tebl/RC-ONE/software/examples/FBK-Movit/movit.pdf

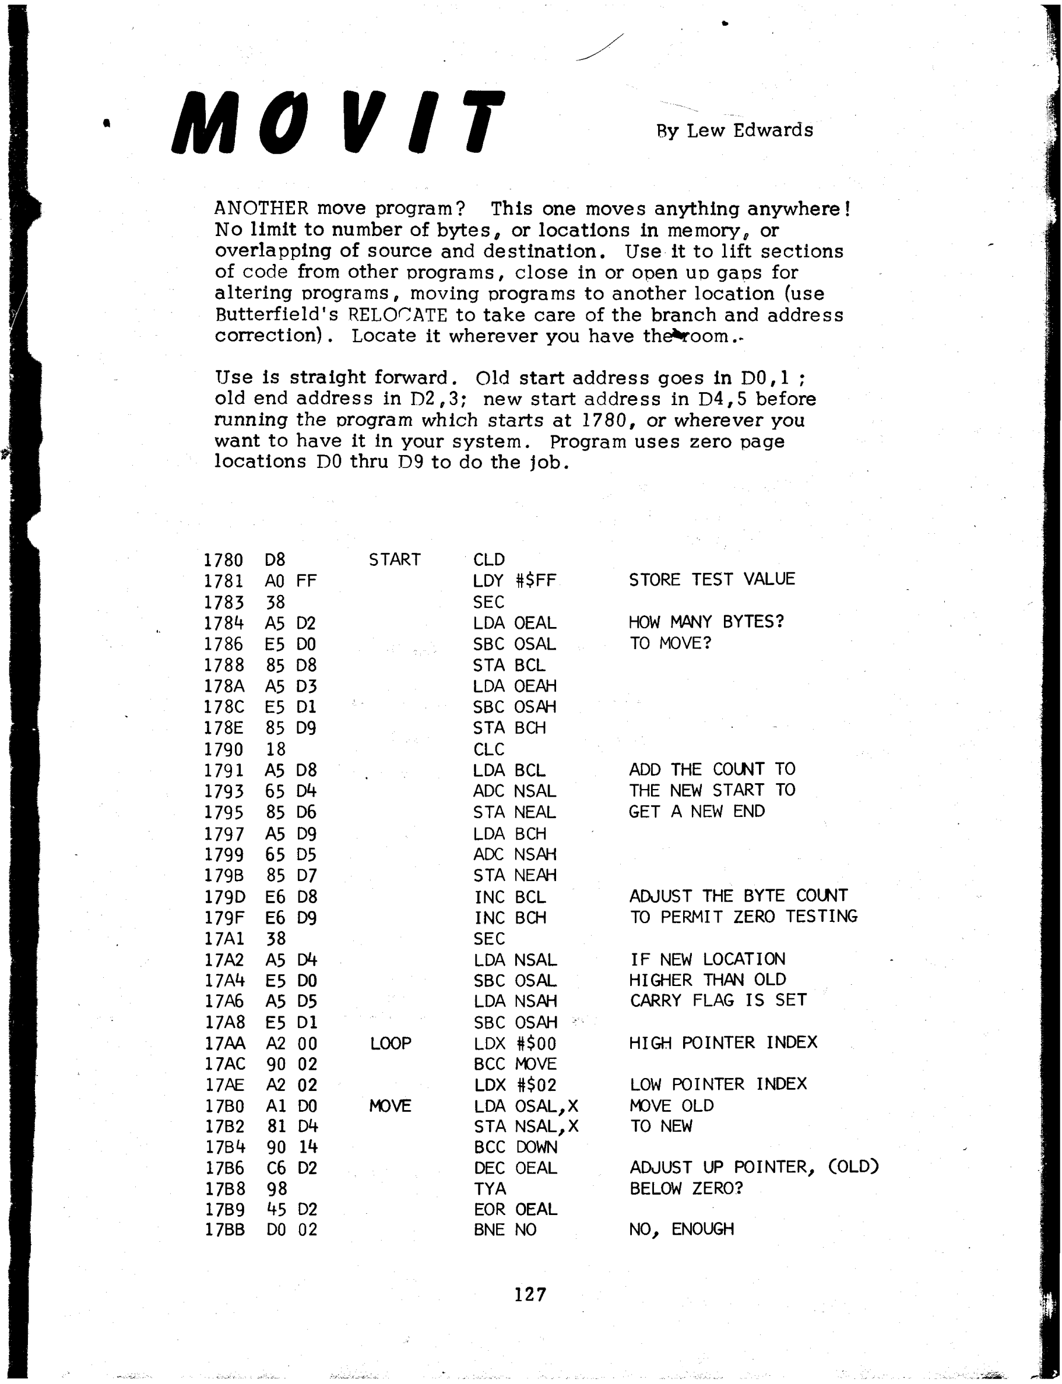
[picture p11: page 1]
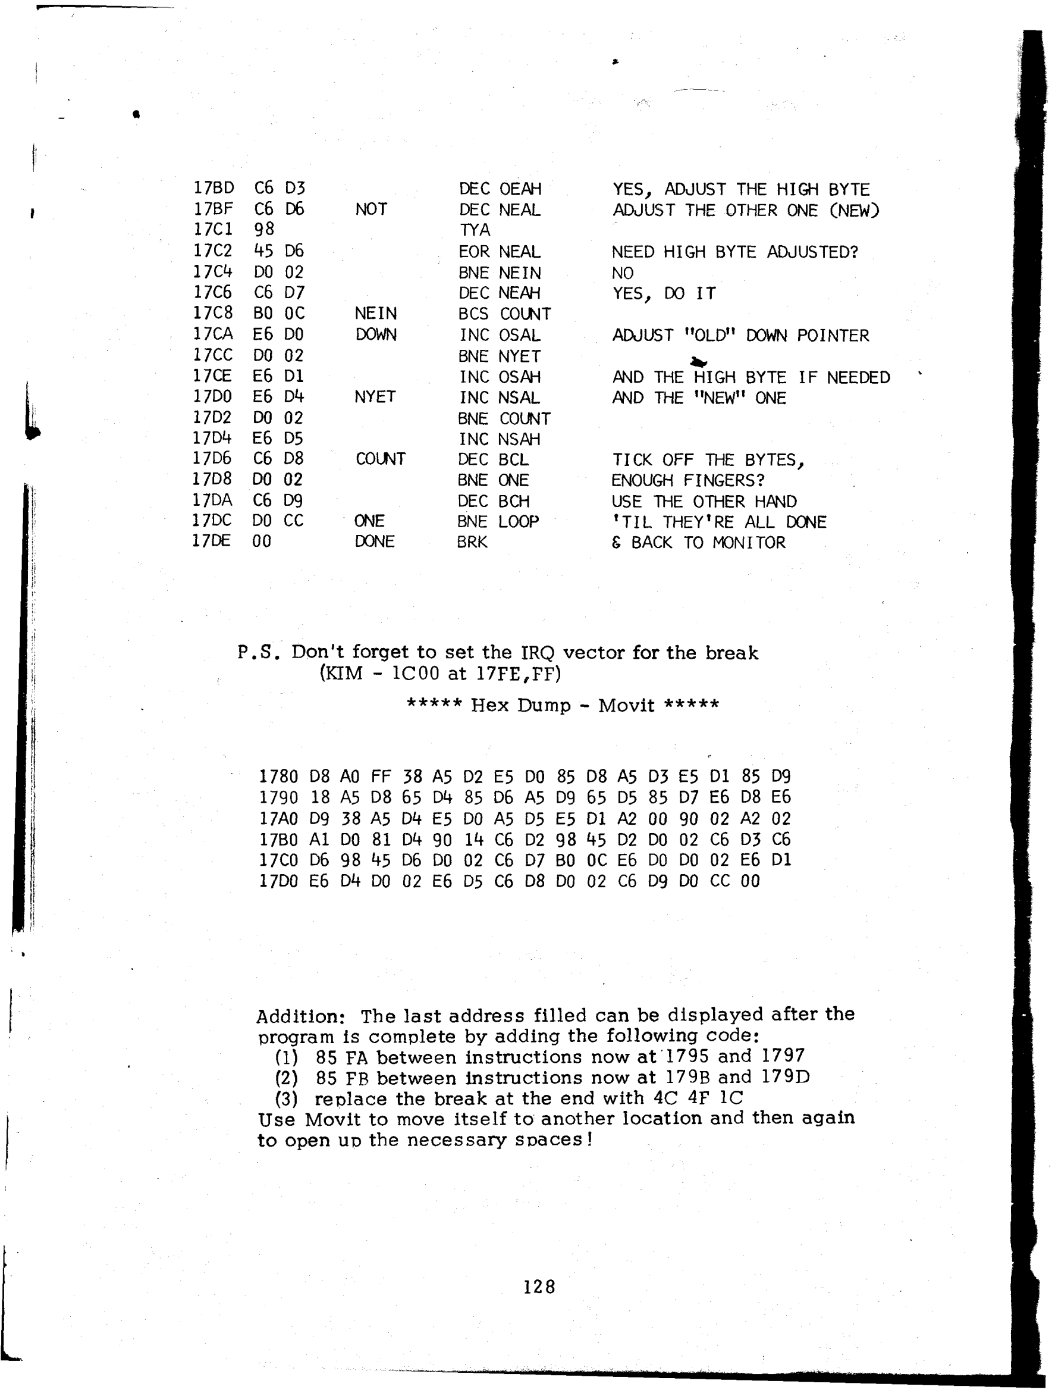
[picture p12: page 2]
