tebl/RC-ONE/gallery/2019-10-24 20.48.41.jpg

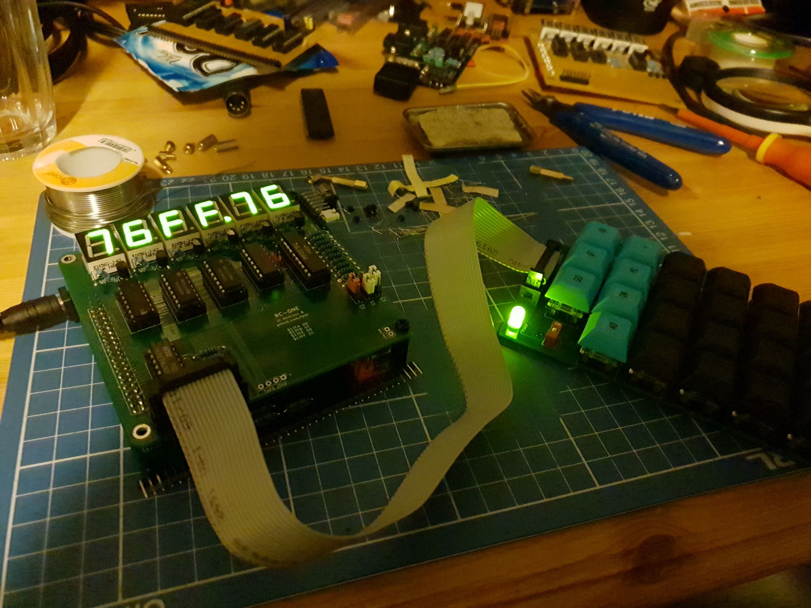
gallery/2019-10-24 20.48.41.jpg
