tebl/RC-ONE/gallery/2019-11-24 02.01.32.jpg

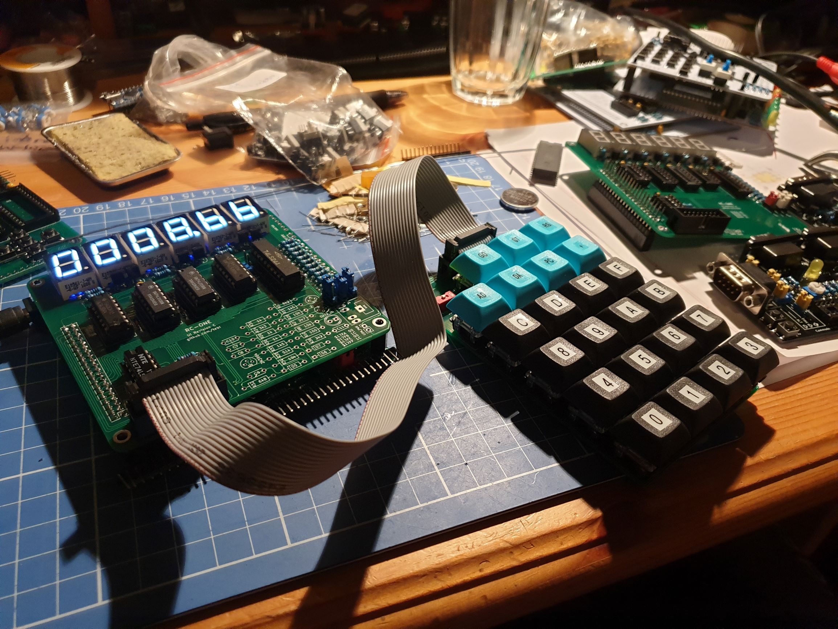
gallery/2019-11-24 02.01.32.jpg
