tebl/RC-ONE/RC1 8K ExRAM/gallery/Annotation 2020-01-12 215217.png

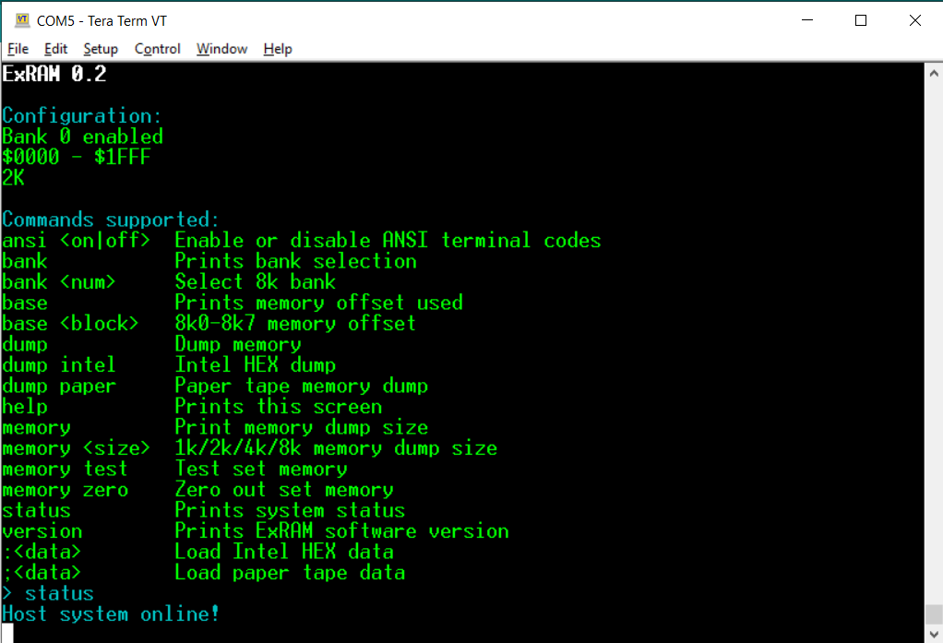
RC1 8K ExRAM/gallery/Annotation 2020-01-12 215217.png
