tebl/RC-ONE/RC1 8K ExRAM/gallery/Annotation 2020-01-12 215605.png

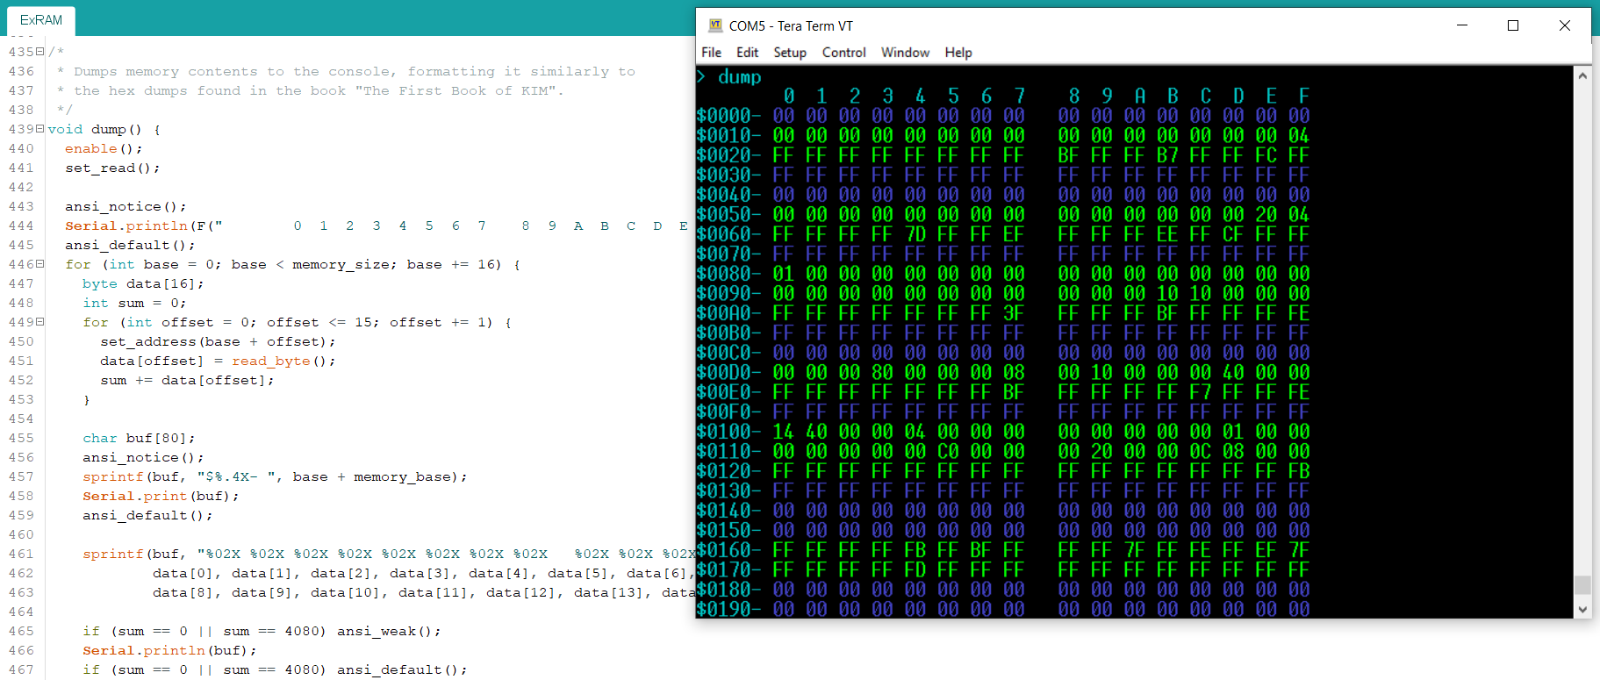
RC1 8K ExRAM/gallery/Annotation 2020-01-12 215605.png
