tebl/RC-ONE/RC1 8K ExRAM/gallery/Annotation 2020-01-13 213625.png

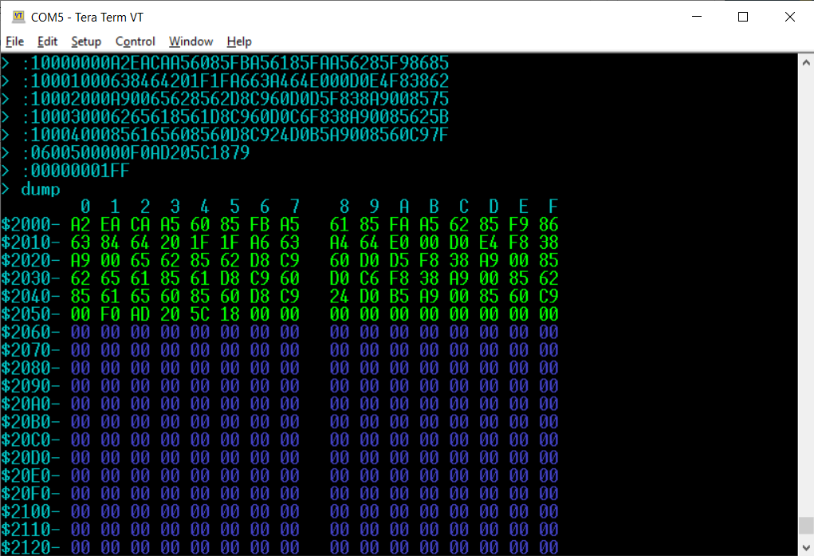
RC1 8K ExRAM/gallery/Annotation 2020-01-13 213625.png
