tebl/RC-ONE/RC1 8K ExRAM/gallery/RC1 8K ExRAM.png

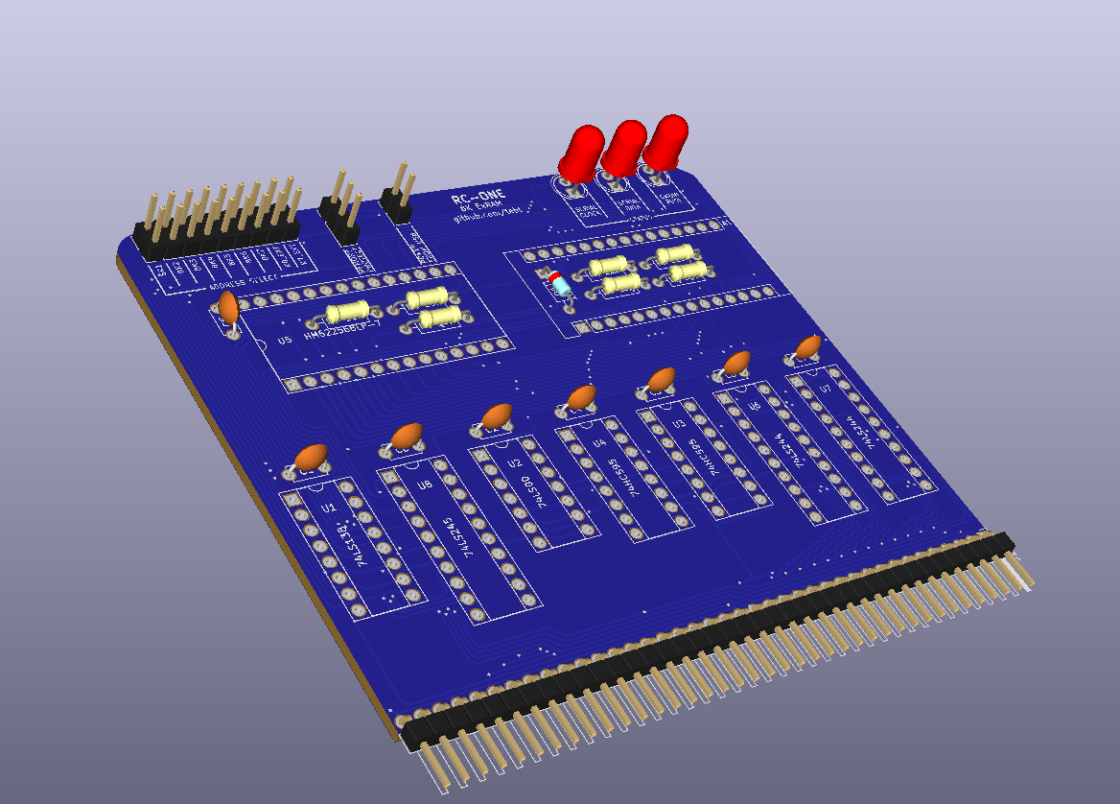
RC1 8K ExRAM/gallery/RC1 8K ExRAM.png
