tebl/RC-ONE/RC1 65K Expansion/gallery/application_io.png

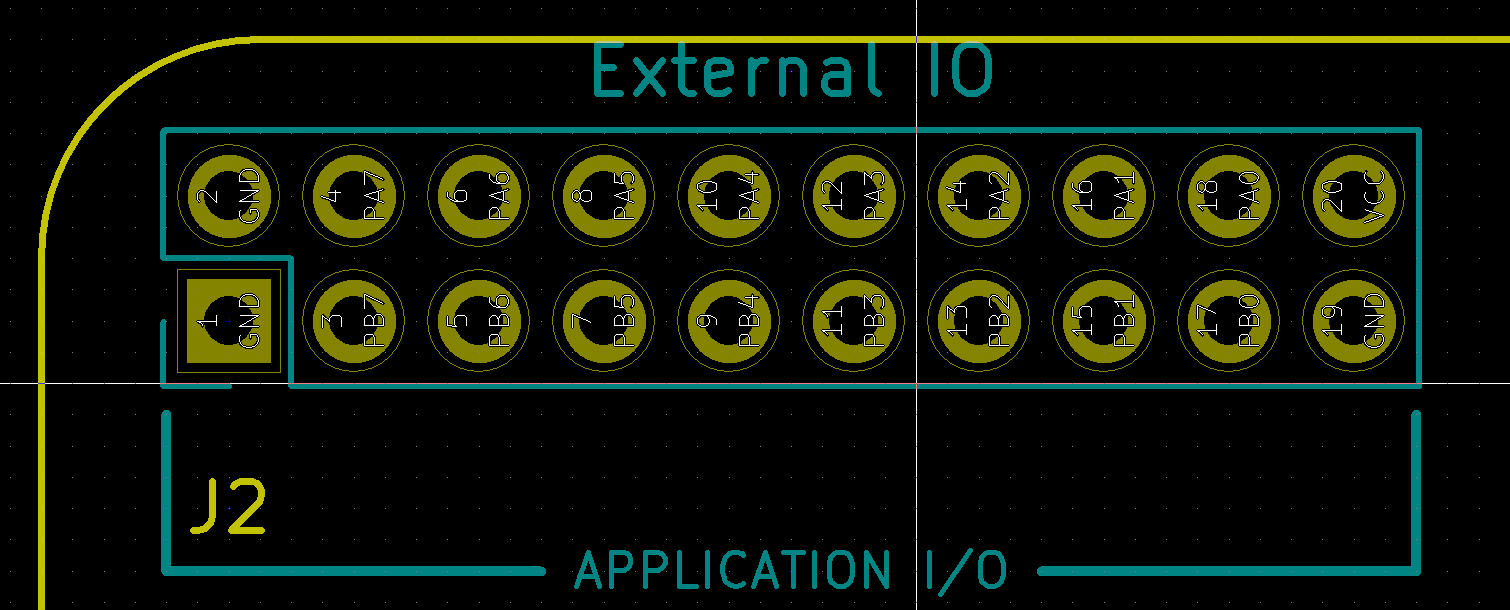
RC1 65K Expansion/gallery/application_io.png
