tebl/RC-ONE/RC1 65K Expansion/gallery/RC1 65K Expansion.png

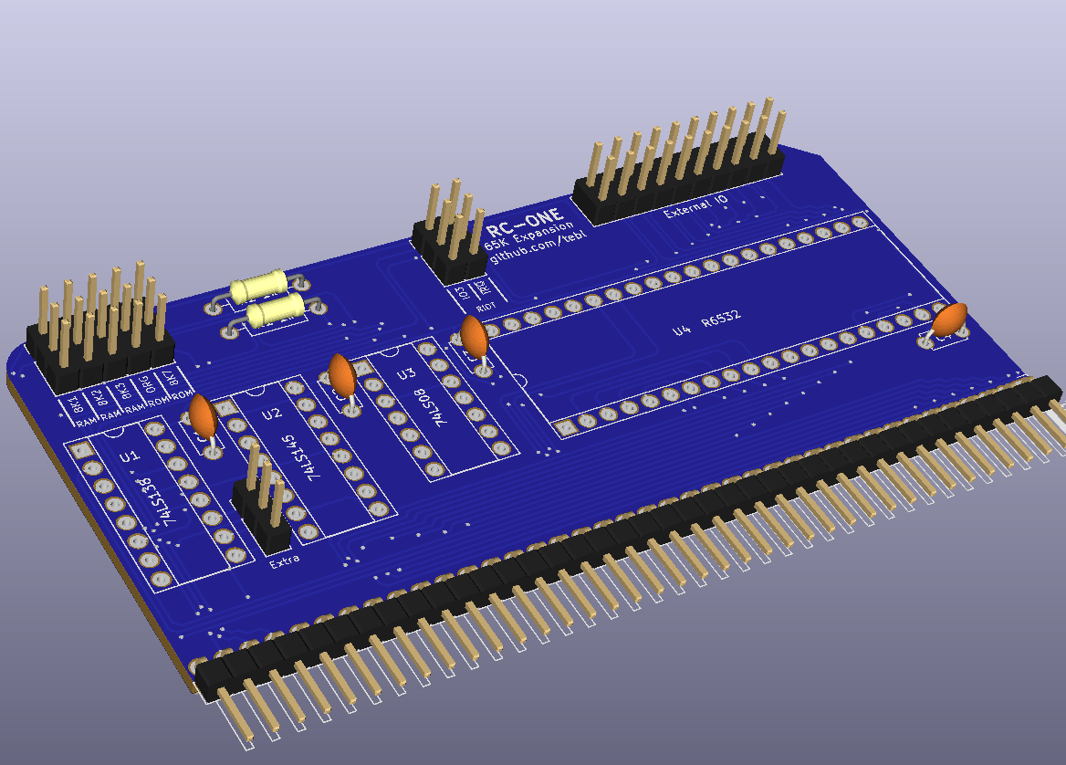
RC1 65K Expansion/gallery/RC1 65K Expansion.png
