tebl/RC-ONE/RC1 ACIA/gallery/2020-10-18 02.24.50.jpg

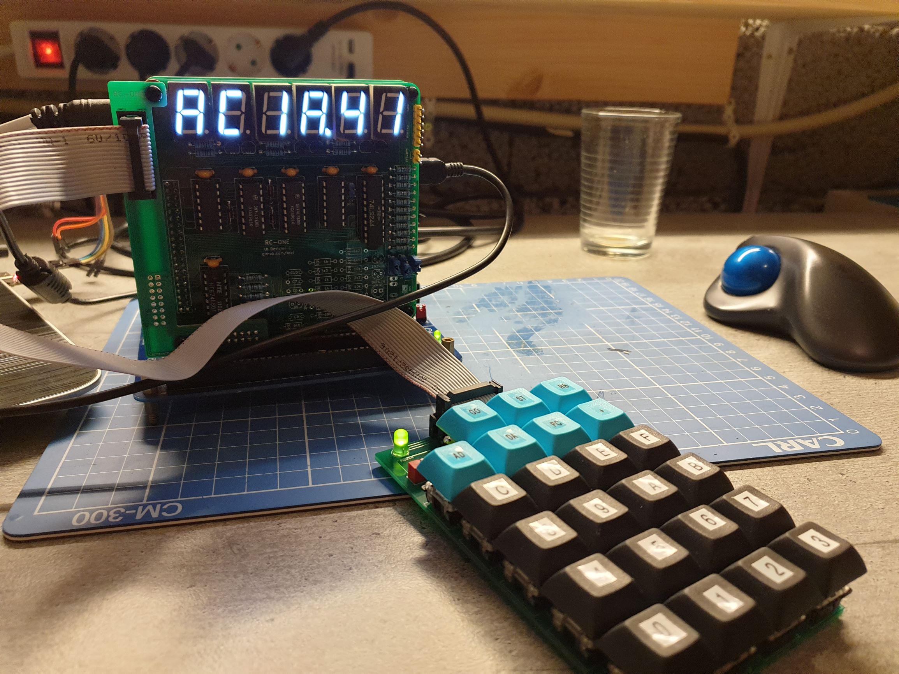
RC1 ACIA/gallery/2020-10-18 02.24.50.jpg
