tebl/RC-ONE/RC1 ACIA/gallery/tera_term_001.png

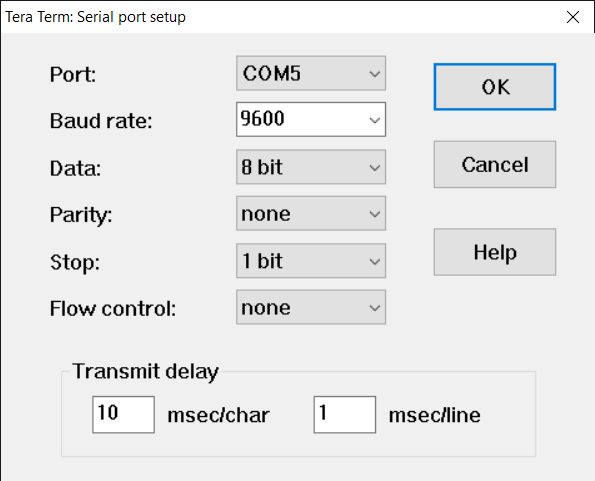
RC1 ACIA/gallery/tera_term_001.png
