tebl/RC-ONE/RC1 ACIA/gallery/tera_term_002.png

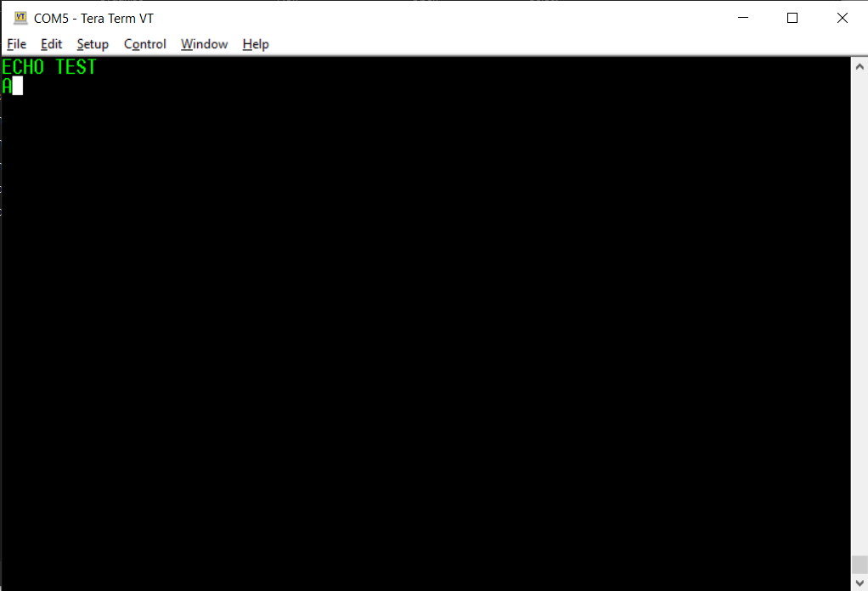
RC1 ACIA/gallery/tera_term_002.png
