tebl/RC-ONE/RC1 CPU/gallery/2019-10-21 21.03.31.jpg

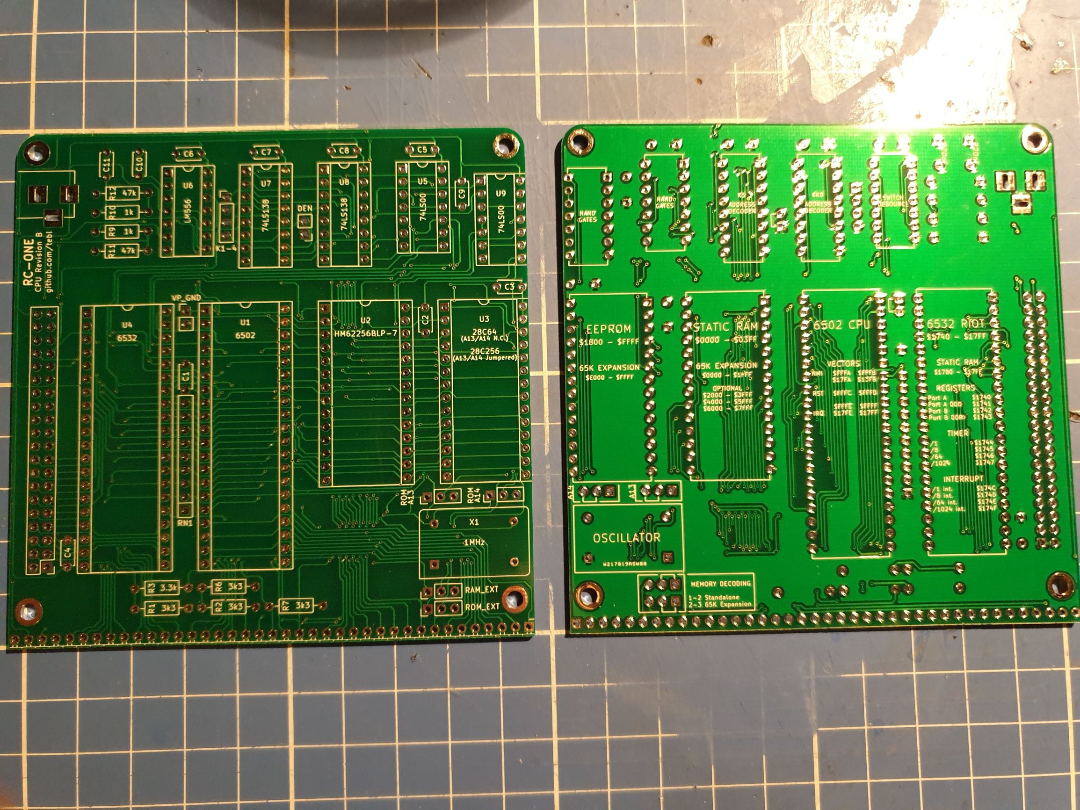
RC1 CPU/gallery/2019-10-21 21.03.31.jpg
