tebl/RC-ONE/RC1 Keypad MX/gallery/2019-10-21 21.00.52.jpg

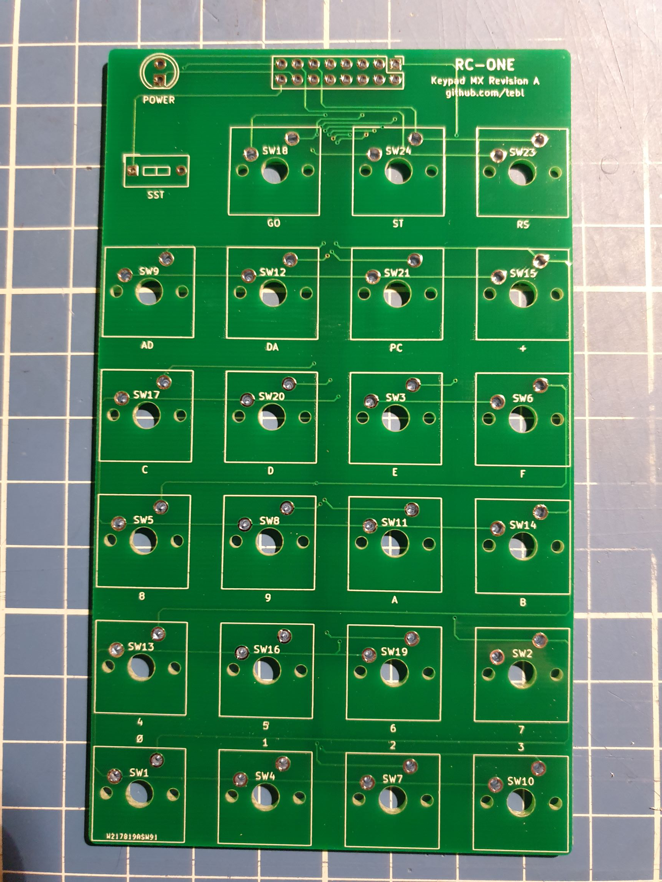
RC1 Keypad MX/gallery/2019-10-21 21.00.52.jpg
