tebl/RC-ONE/RC1 Sound Interface/gallery/RC1 Sound Interface #2.png

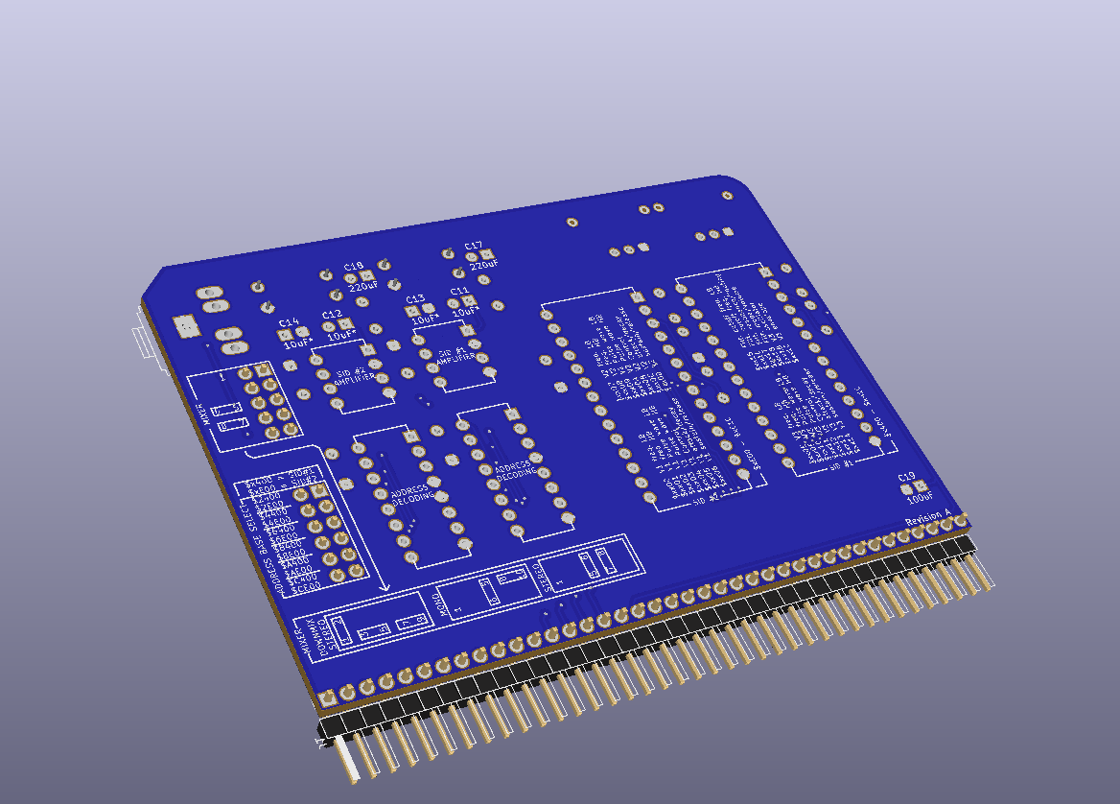
RC1 Sound Interface/gallery/RC1 Sound Interface #2.png
