tebl/RC-ONE/RC1 UI/gallery/2019-10-21 21.02.37.jpg

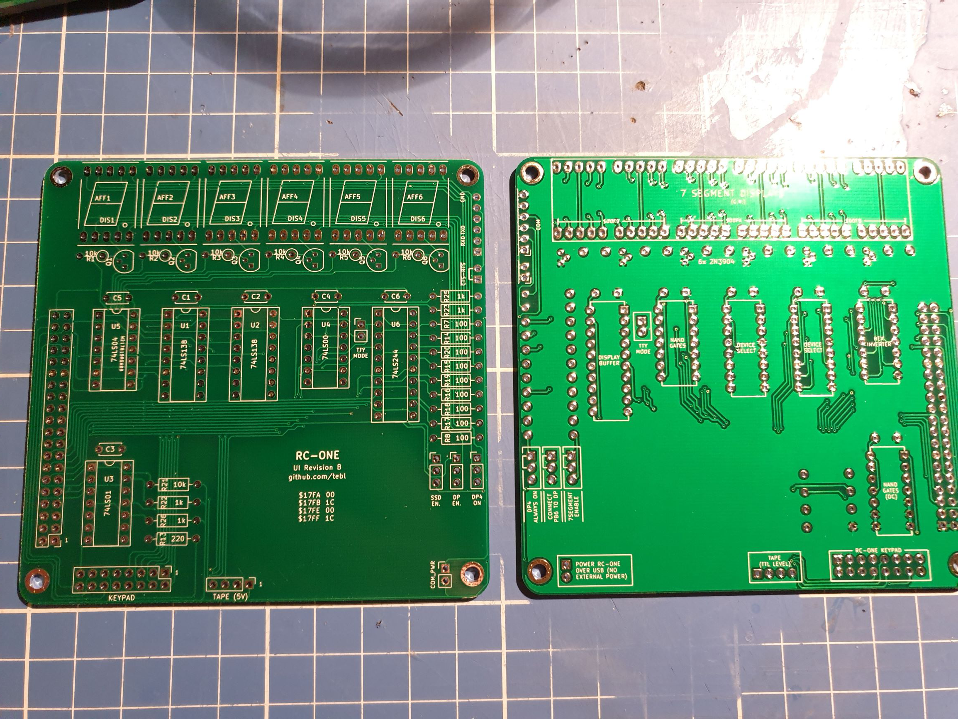
RC1 UI/gallery/2019-10-21 21.02.37.jpg
