tebl/RC-ONE/RC1 Keypad/export/RC1 Keypad.pdf

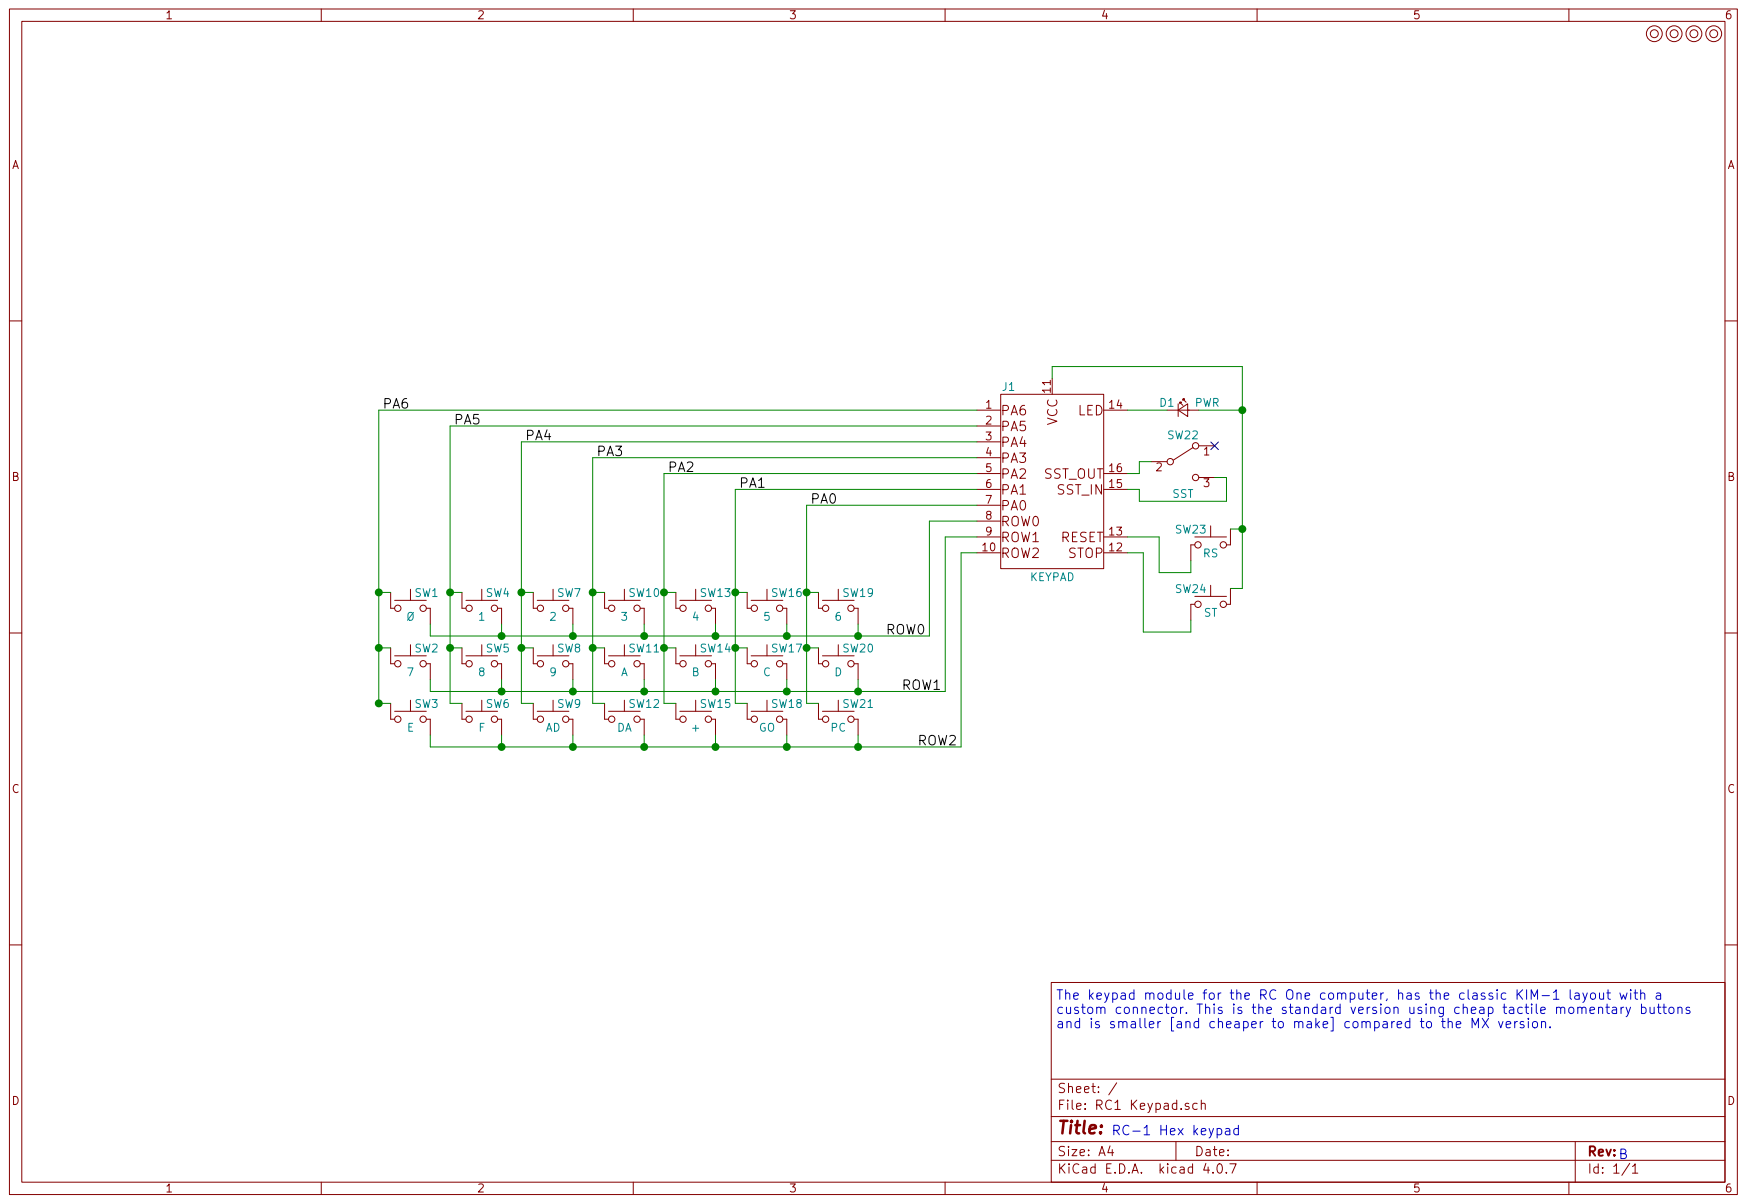
[picture p54: page 1]
