tebl/RC-ONE/RC1 CPU/export/RC1 CPU.pdf

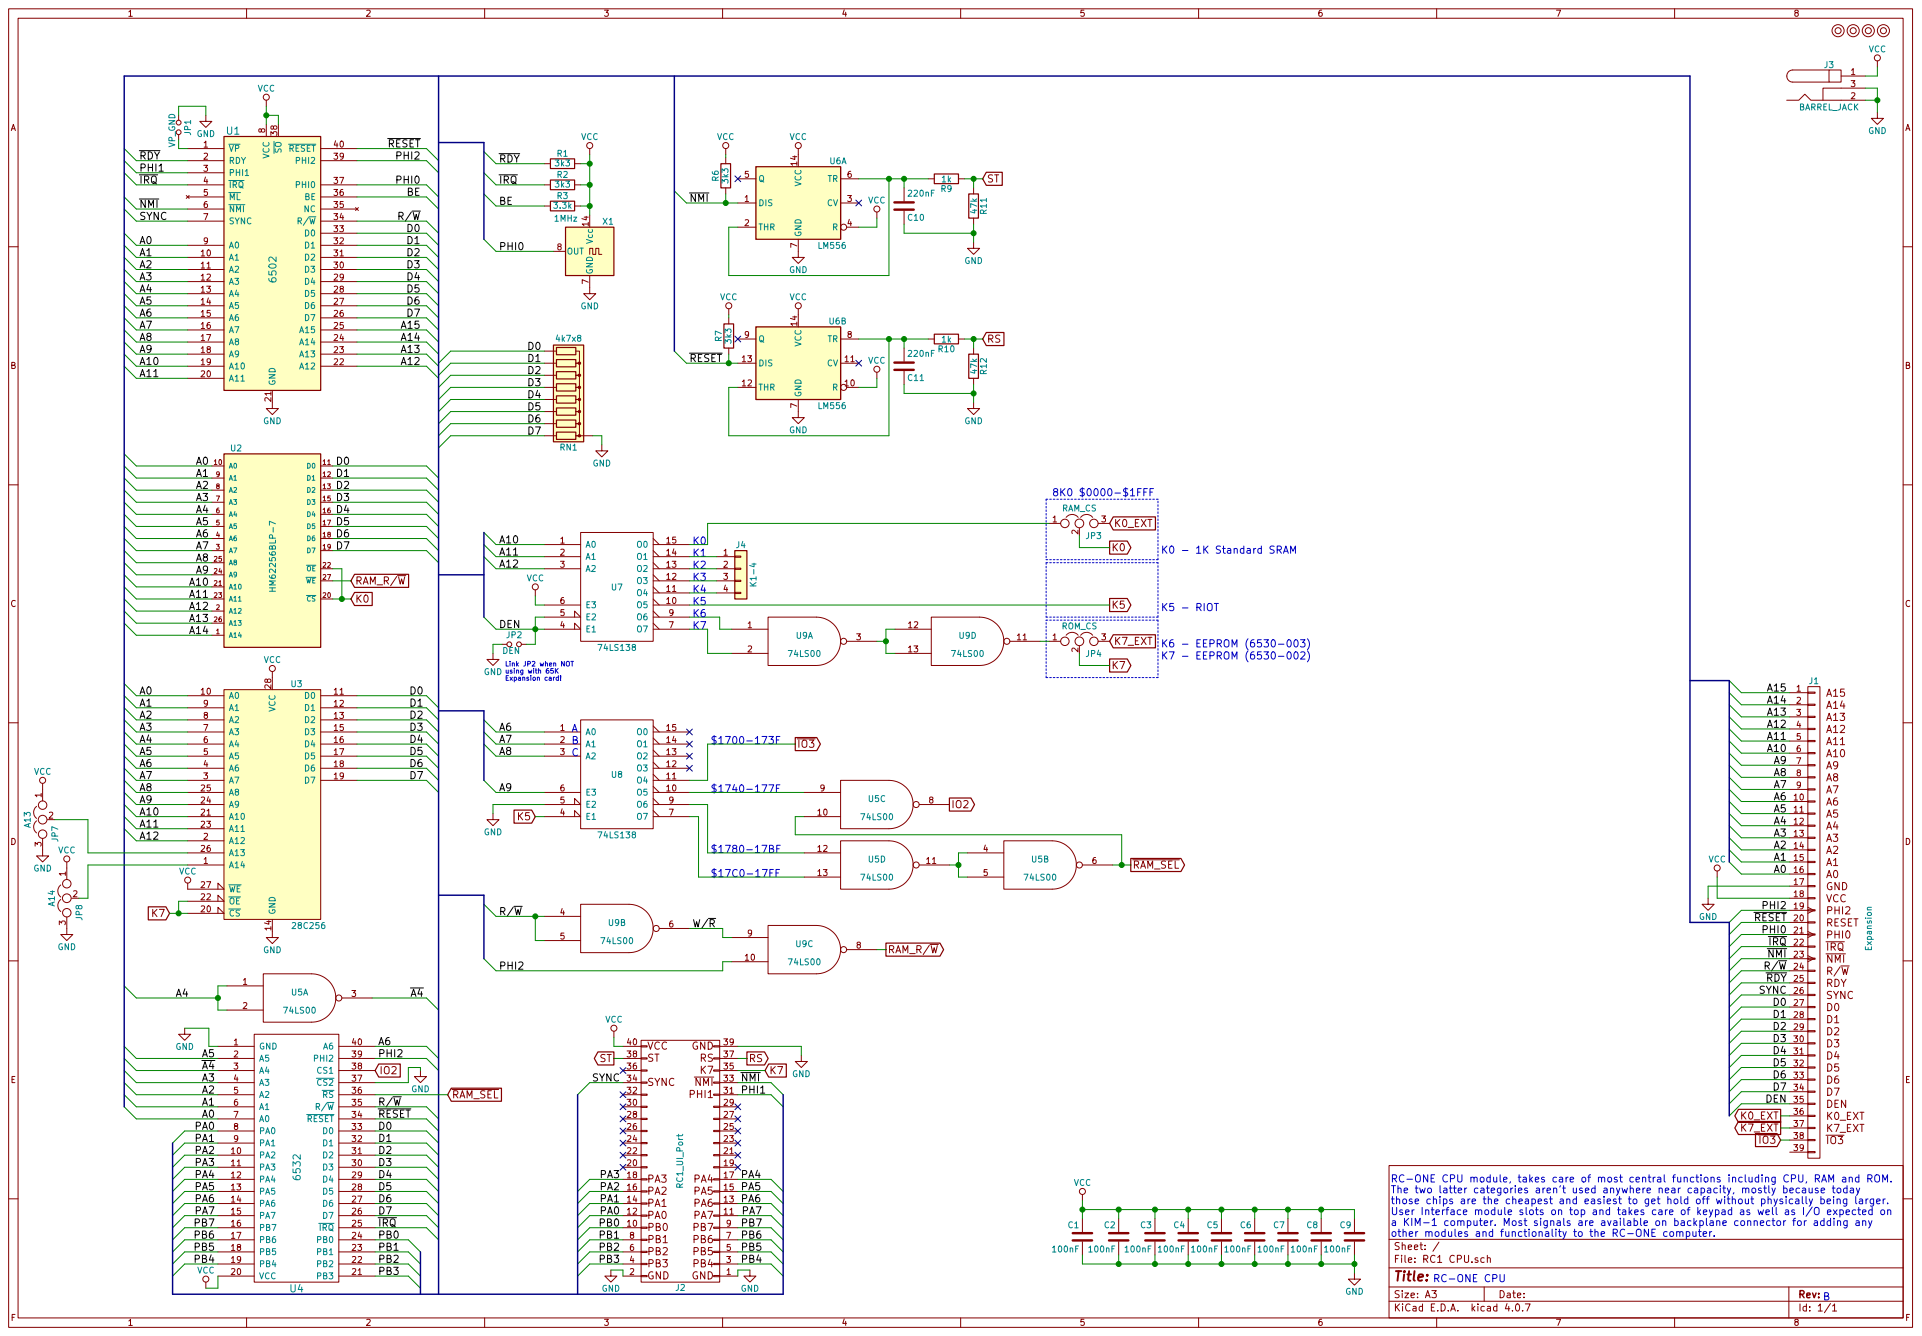
[picture p55: page 1]
