tebl/RC-ONE/RC1 UI/RC1 UI.kicad_pcb

## KiCad design RC1 UI/RC1 UI.kicad_pcb (2019-11-08)

Schematic: RC1 UI-2020-03-10-23-34-16.sch

Parts:
AFF1: DIS1; 7SegmentLED_LTS6760_LTS6780
AFF2: DIS2; 7SegmentLED_LTS6760_LTS6780
AFF3: DIS3; 7SegmentLED_LTS6760_LTS6780
AFF4: DIS4; 7SegmentLED_LTS6760_LTS6780
AFF5: DIS5; 7SegmentLED_LTS6760_LTS6780
AFF6: DIS6; 7SegmentLED_LTS6760_LTS6780
C1, C2, C3, C4, C5, C6, C11: 100nF; C_Disc_D4.7mm_W2.5mm_P5.00mm
C7, C9: 50nF; C_Disc_D4.7mm_W2.5mm_P5.00mm
C8: 68nF; C_Disc_D4.7mm_W2.5mm_P5.00mm
C10: 500nF; C_Disc_D4.7mm_W2.5mm_P5.00mm
D1, D2, D3: 1n4148; D_DO-35_SOD27_P7.62mm_Horizontal
D4: DATA_IN; LED_D5.0mm
D5, D6, D7: 1n914; D_DO-35_SOD27_P7.62mm_Horizontal
J1: KEYPAD; Pin_Header_Straight_2x08_Pitch2.54mm
J2: RC1_UI_Port; Pin_Header_Straight_2x20_Pitch2.54mm
J3: COM; Pin_Header_Angled_1x06_Pitch2.54mm
J4: TAPE; Tayda_3.5mm_stereo_TRS_jack_A-853
JP1: COM_PWR; Pin_Header_Straight_1x02_Pitch2.54mm
JP2: FlowControl; Pin_Header_Angled_1x02_Pitch2.54mm
JP3: USE_COM; Pin_Header_Straight_1x02_Pitch2.54mm
JP4: DP_EN; Pin_Header_Straight_1x03_Pitch2.54mm
JP5: SSD_EN; Pin_Header_Straight_1x03_Pitch2.54mm
JP6: DP4_EN; Pin_Header_Straight_1x03_Pitch2.54mm
M1, M2, M3, M4: Mounting; 1pin
Q1, Q2, Q3, Q4, Q5, Q6, Q7, Q8, Q9: 2N3904; TO-92_Molded_Narrow
R1, R2, R3, R4, R5, R6, R9, R21, R28, R34: 10k; R_Axial_DIN0207_L6.3mm_D2.5mm_P10.16mm_Horizontal
R7, R8, R10, R14, R15, R16, R17, R18, R19, R20: 100; R_Axial_DIN0207_L6.3mm_D2.5mm_P10.16mm_Horizontal
R11, R33: 1k5; R_Axial_DIN0207_L6.3mm_D2.5mm_P10.16mm_Horizontal
R12: 6k2; R_Axial_DIN0207_L6.3mm_D2.5mm_P10.16mm_Horizontal
R13: 220; R_Axial_DIN0207_L6.3mm_D2.5mm_P10.16mm_Horizontal
R22, R23, R25, R26, R29, R30, R31: 1k; R_Axial_DIN0207_L6.3mm_D2.5mm_P10.16mm_Horizontal
R24: 3k3; R_Axial_DIN0207_L6.3mm_D2.5mm_P10.16mm_Horizontal
R27: 2k7; R_Axial_DIN0207_L6.3mm_D2.5mm_P10.16mm_Horizontal
R32: 6k8; R_Axial_DIN0207_L6.3mm_D2.5mm_P10.16mm_Horizontal
R35: 51k; R_Axial_DIN0207_L6.3mm_D2.5mm_P10.16mm_Horizontal
R36: 2k2; R_Axial_DIN0207_L6.3mm_D2.5mm_P10.16mm_Horizontal
U1, U2: 74LS138; DIP-16_W7.62mm_Socket
U3: 74LS01; DIP-14_W7.62mm_Socket
U4: 74LS00; DIP-14_W7.62mm_Socket
U5: 74LS04; DIP-14_W7.62mm_Socket
U6: 74LS244; DIP-20_W7.62mm_Socket

Connections:
/A: AFF1.7, AFF2.7, AFF3.7, AFF4.7, AFF5.7, AFF6.7, R14.2
/B: AFF1.6, AFF2.6, AFF3.6, AFF4.6, AFF5.6, AFF6.6, R15.2
/C: AFF1.4, AFF2.4, AFF3.4, AFF4.4, AFF5.4, AFF6.4, R16.2
/D: AFF1.2, AFF2.2, AFF3.2, AFF4.2, AFF5.2, AFF6.2, R17.2
/DIS1: R1.2, U5.2
/DIS2: R2.2, U5.4
/DIS3: R3.2, U5.6
/DIS4: R4.2, U5.8
/DIS5: R5.2, U5.10
/DIS6: R6.2, U5.12
/DP: AFF1.5, AFF2.5, AFF3.5, AFF5.5, AFF6.5, JP6.3, R7.2
/DP4: AFF4.5, JP6.2
/E: AFF1.1, AFF2.1, AFF3.1, AFF4.1, AFF5.1, AFF6.1, R18.2
/F: AFF1.9, AFF2.9, AFF3.9, AFF4.9, AFF5.9, AFF6.9, R19.2
/G: AFF1.10, AFF2.10, AFF3.10, AFF4.10, AFF5.10, AFF6.10, R20.2
/KP_RS: J1.13, J2.37
/KP_ST: J1.12, J2.38
/MODE: JP3.2, U1.12 (O3)
/PA0: J1.7, J2.12, JP3.1, U6.2 (I0a)
/PA1: J1.6, J2.14, U6.4 (I1a)
/PA2: J1.5, J2.16, U6.6 (I2a)
/PA3: J1.4, J2.18, U6.8 (I3a)
/PA4: J1.3, J2.17, U6.11 (I0b)
/PA5: J1.2, J2.15, U6.13 (I1b)
/PA6: J1.1, J2.13, U6.15 (I2b)
/PA7: J2.11, U4.6, U4.9
/PB0: J2.10, U4.10
/PB1: J2.8, U1.1 (A0), U2.1 (A0)
/PB2: J2.6, U1.2 (A1), U2.2 (A1)
/PB3: J2.4, U1.3 (A2), U2.3 (A2)
/PB4: J2.3, U1.5 (E2), U2.6 (E3)
/PB5: J2.5, U4.1, U4.2
/PB6: J2.7, JP4.1
/PB7: J2.9, U3.12, U4.11
/ROW0: D3.2, J1.8
/ROW1: D2.2, J1.9
/ROW2: D1.2, J1.10
/RX: R25.1, U4.5
/TAPE_EAR: C11.2, J4.2, J4.3
/TAPE_MIC: J4.4, J4.5, R9.1, R10.1
/TX: R23.1, U4.8
FROM_TAPE: Q7.3, R11.1, U4.13
K7: J2.35, U3.2
unnamed: AFF1.3, AFF1.8, Q1.3
unnamed: AFF2.3, AFF2.8, Q2.3
unnamed: AFF3.3, AFF3.8, Q3.3
unnamed: AFF4.3, AFF4.8, Q4.3
unnamed: AFF5.3, AFF5.8, Q5.3
unnamed: AFF6.3, AFF6.8, Q6.3
unnamed: C7.2, R29.1, R30.2
unnamed: C8.2, R30.1, R31.2
unnamed: C9.2, D5.1, R31.1, R32.1
unnamed: C10.1, D5.2, D6.1
unnamed: C10.2, Q9.3, R33.1
unnamed: C11.1, R36.2
unnamed: D1.1, U1.13 (O2)
unnamed: D2.1, U1.14 (O1)
unnamed: D3.1, U1.15 (O0)
unnamed: D4.1, Q8.3, R24.1
unnamed: D4.2, R27.1
unnamed: D7.1, Q9.2, R34.1, R35.2, R36.1
unnamed: J1.14, R13.1
unnamed: J3.1, JP2.1
unnamed: J3.2, R23.2
unnamed: J3.3, R25.2
unnamed: J3.4, JP1.1
unnamed: J3.5, JP2.2
unnamed: JP4.2, U6.17 (I3b)
unnamed: JP5.2, U6.1 (OEa), U6.19 (OEb)
unnamed: JP6.1, R8.2
unnamed: Q1.2, R1.1
unnamed: Q2.2, R2.1
unnamed: Q3.2, R3.1
unnamed: Q4.2, R4.1
unnamed: Q5.2, R5.1
unnamed: Q6.2, R6.1
unnamed: Q7.2, R12.1, R24.2
unnamed: Q8.2, R28.2, R29.2
unnamed: R7.1, U6.3 (O3b)
unnamed: R14.1, U6.18 (O0a)
unnamed: R15.1, U6.16 (O1a)
unnamed: R16.1, U6.14 (O2a)
unnamed: R17.1, U6.12 (O3a)
unnamed: R18.1, U6.9 (O0b)
unnamed: R19.1, U6.7 (O1b)
unnamed: R20.1, U6.5 (O2b)
unnamed: R26.2, U3.4, U3.10
unnamed: U1.7 (O7), U5.9
unnamed: U1.9 (O6), U5.5
unnamed: U1.10 (O5), U5.3
unnamed: U1.11 (O4), U5.1
unnamed: U2.14 (O1), U5.13
unnamed: U2.15 (O0), U5.11
unnamed: U4.3, U4.4, U4.12
SST_IN: J1.15, R21.1, U3.1
SST_OUT: J1.16, J2.33
SYNC: J2.34, U3.3
TO_TAPE: R9.2, R22.1, U3.13
VCC: C1.1, C2.1, C3.1, C4.1, C5.1, C6.1, J1.11, J2.40, JP1.2, JP5.3, R8.1, R11.2, R21.2, R22.2, R26.1, R27.2, R33.2, R35.1, U1.6 (E3), U1.16 (VCC), U2.16 (VCC), U3.11, U3.14 (VCC), U4.14 (VCC), U5.14 (VCC), U6.20 (VCC)

Notes on the sheet:
RC-ONE User Interface
RC-ONE User Interface module, slots into CPU board with the connector doubling as an expansion port (not all signals are used). Includes keypad connector, output as well as a secondary mode over serial (FTDI module). Plenty of space left over, in the future this will hopefully be filled up by tape 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
KIM-1s 6530 didn't have a PB6, but using it for the DP.
TTY/TAPE CONTROL
TAPE
TTY DATA OUT
TTY DATA IN
~RTS
RXD
TXD
VCC
~CTS
GND
Uses the same cable setup as found on the ZX Spectrum +3, with EAR is data from tape to computer - MIC is data out to tape.

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
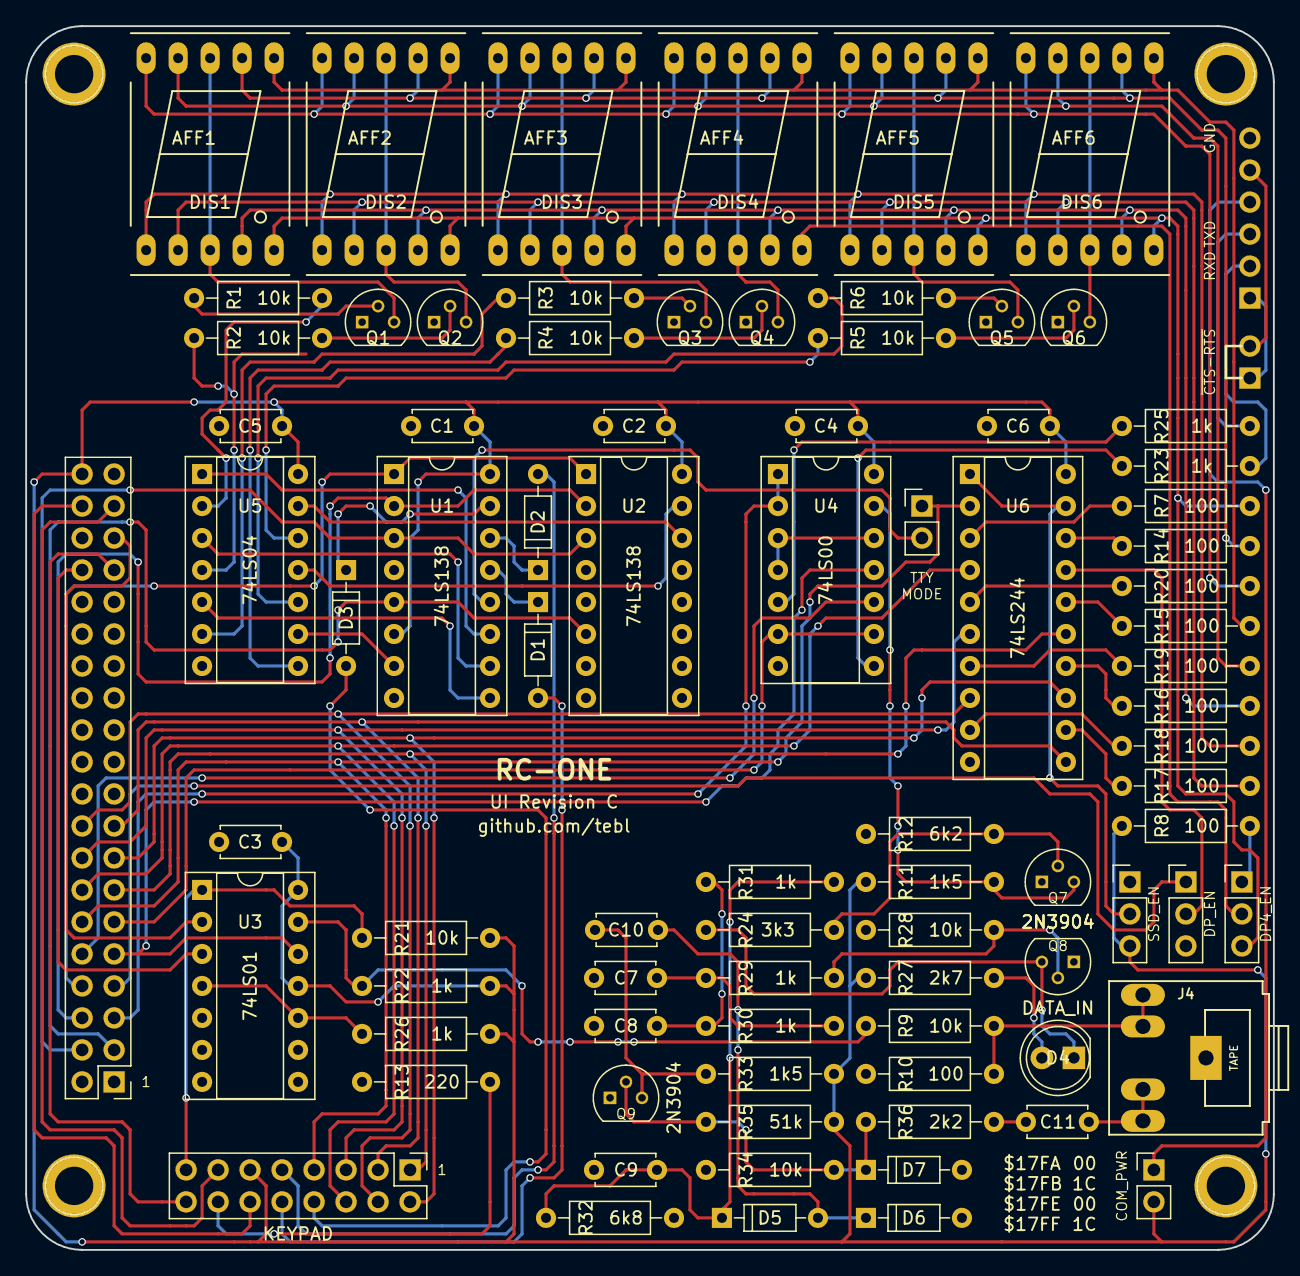
[picture p80: board RC1 UI.kicad_pcb from above]

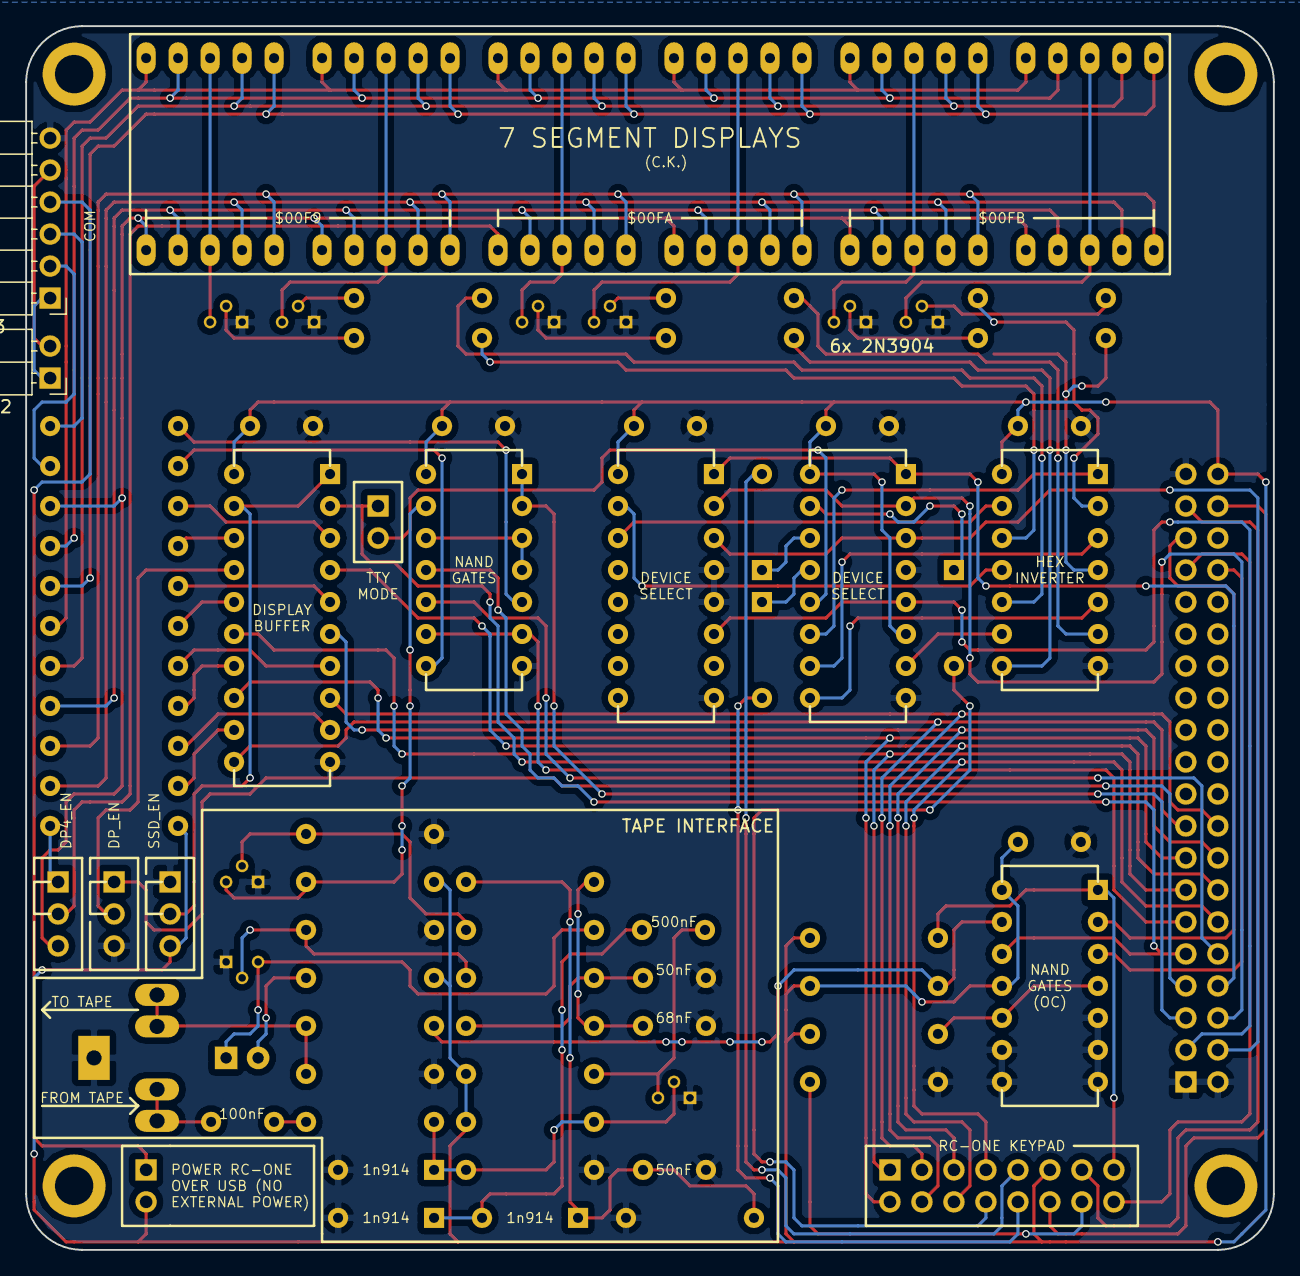
[picture p81: board RC1 UI.kicad_pcb from below]

Board: 2 copper layers, 99.1 x 97.2 mm, 89 parts (2 on the bottom side), 100 nets.
