tebl/RC-ONE/software/arduino/ExRAM/ExRAM/constants.h

#define VERSION "0.3"
#define BAUD_RATE 115200
#define MAX_INPUT_SIZE 100
#define MAX_MEMORY_SIZE 8192
#define TERMINAL_COLS 80
//#define DEBUG

/* Pin definitions */
#define SHIFT_DATA 2
#define SHIFT_CLK 3
#define SHIFT_LATCH 4

#define EX_D0 6
#define EX_D7 13
#define EX_A13 14
#define EX_A14 15
#define EX_RnW 16
#define EX_CS 19

#define EX_CONTROL 5
#define EX_RESET 17
